josdreesen/Lilith_NT/ALU_NT/ALU_NT.jpg

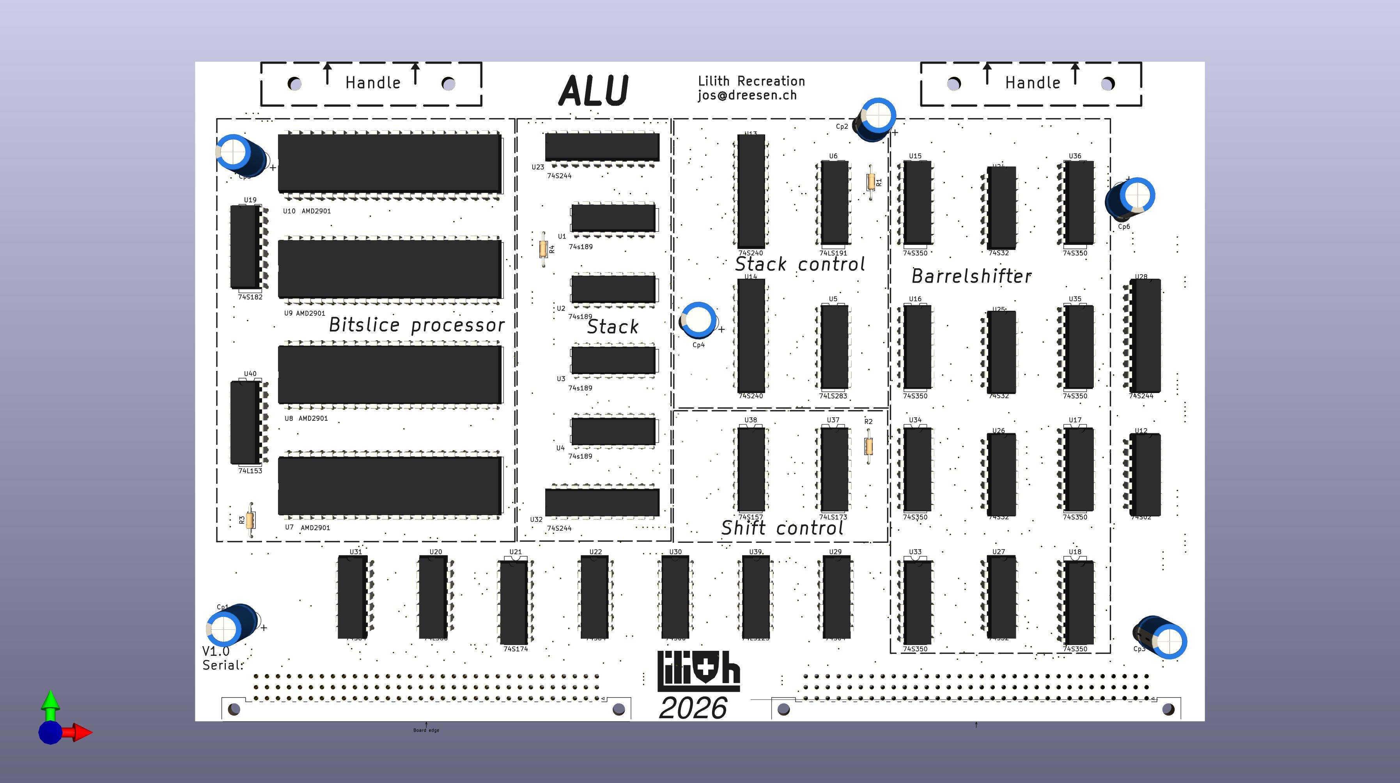
ALU_NT/ALU_NT.jpg
